nbremond77/Autoduino/photos/IMG_6386.resized.JPG

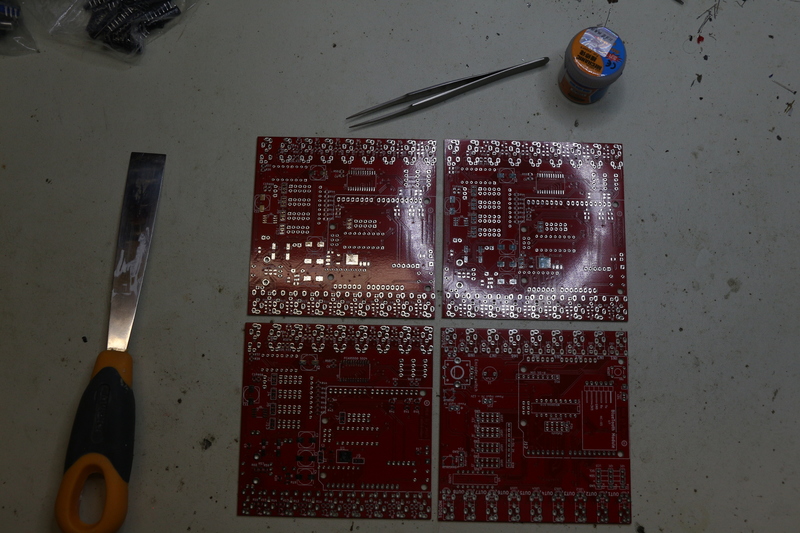
photos/IMG_6386.resized.JPG
