nbremond77/Autoduino/photos/IMG_6387.resized.JPG

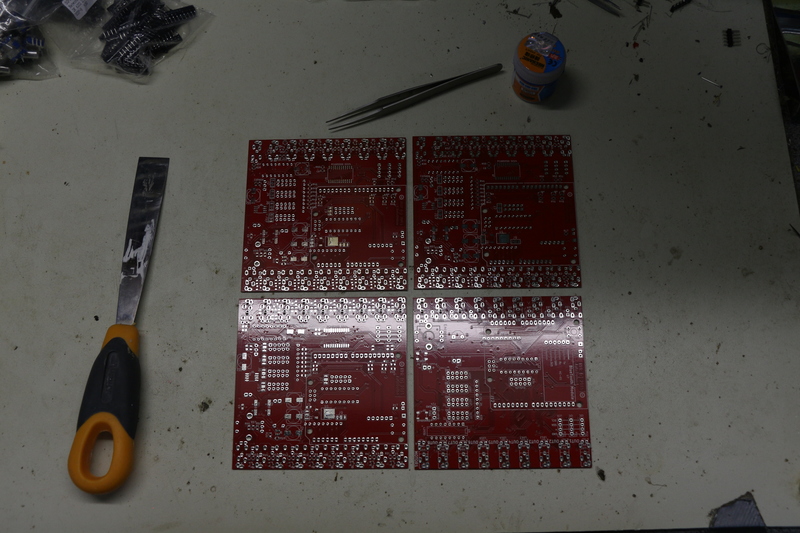
photos/IMG_6387.resized.JPG
