nbremond77/Autoduino/photos/IMG_6388.resized.JPG

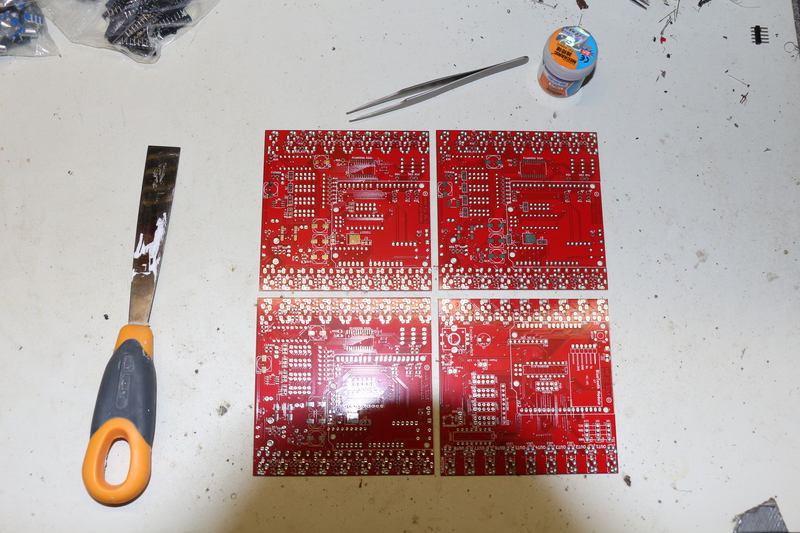
photos/IMG_6388.resized.JPG
