nbremond77/Autoduino/photos/IMG_6389.resized.JPG

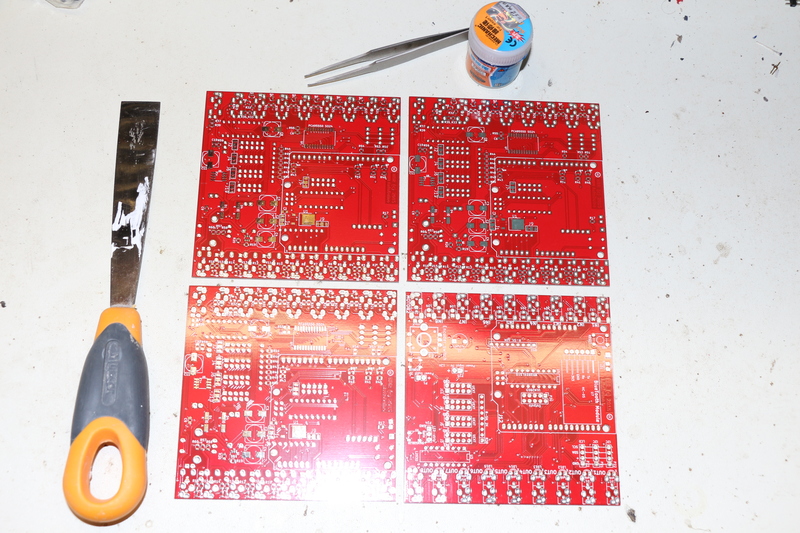
photos/IMG_6389.resized.JPG
