nbremond77/Autoduino/photos/IMG_6390.resized.JPG

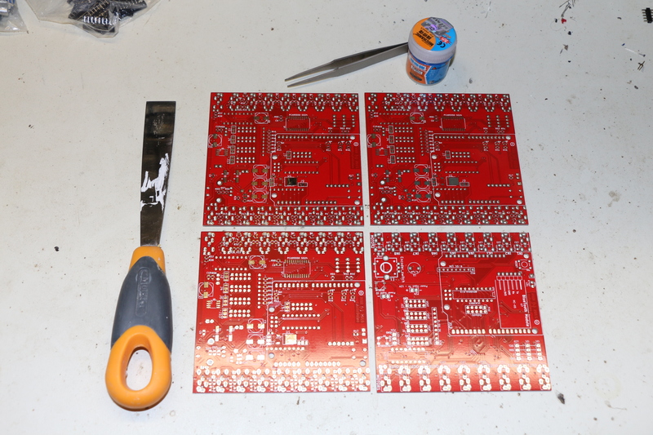
photos/IMG_6390.resized.JPG
