nbremond77/Autoduino/photos/IMG_6391.resized.JPG

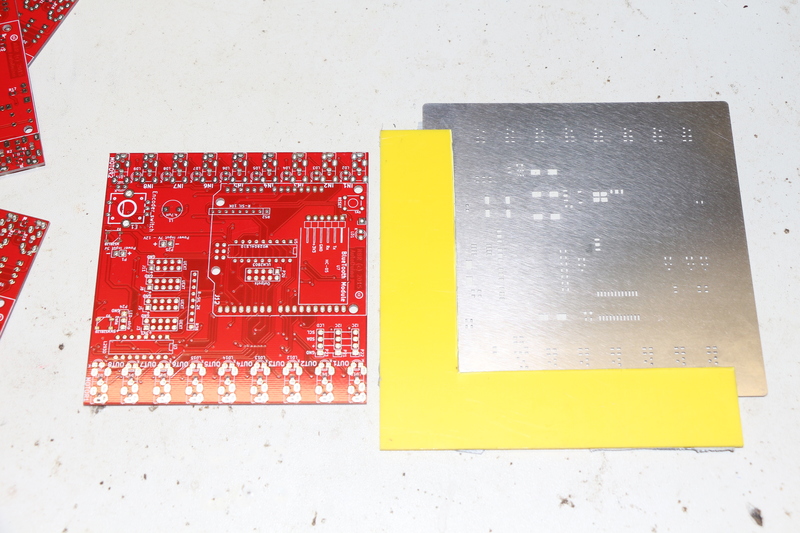
photos/IMG_6391.resized.JPG
