nbremond77/Autoduino/photos/IMG_6392.resized.JPG

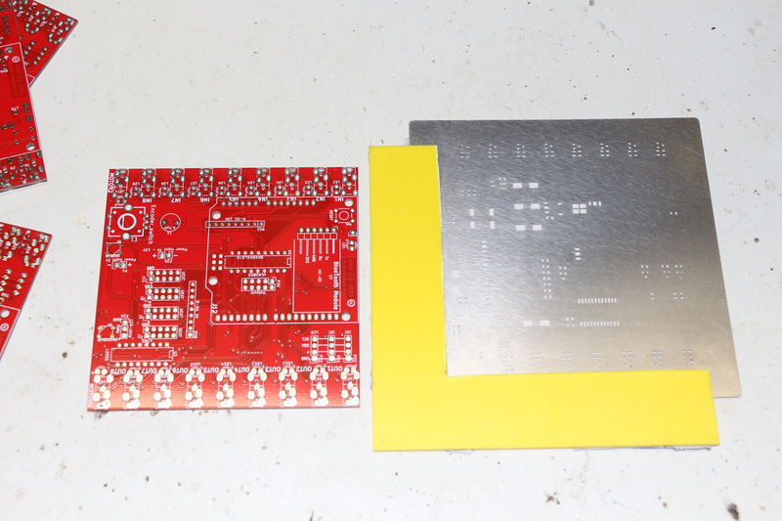
photos/IMG_6392.resized.JPG
