nbremond77/Autoduino/photos/IMG_6393.resized.JPG

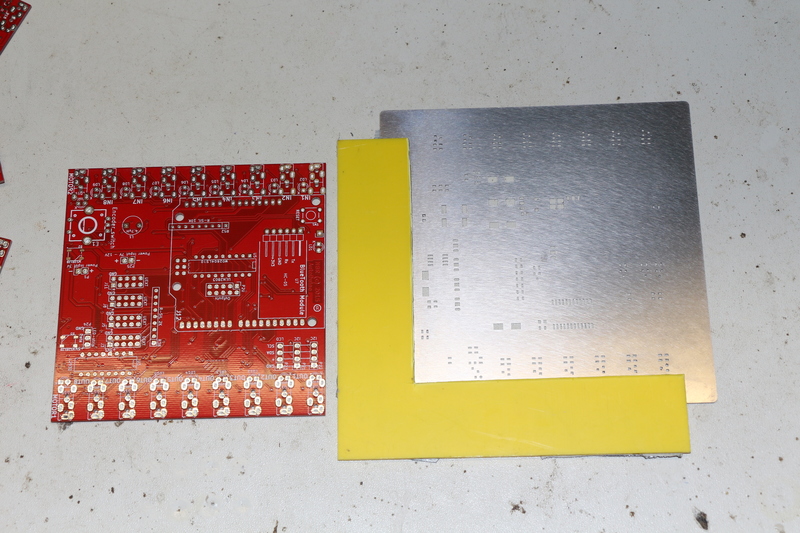
photos/IMG_6393.resized.JPG
