nbremond77/Autoduino/photos/IMG_6394.resized.JPG

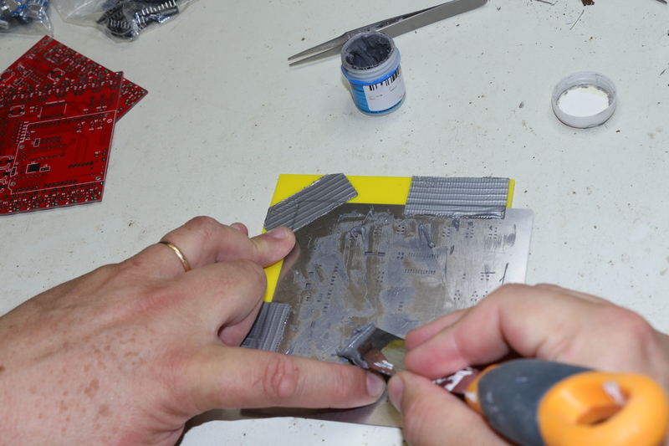
photos/IMG_6394.resized.JPG
