nbremond77/Autoduino/photos/IMG_6395.resized.JPG

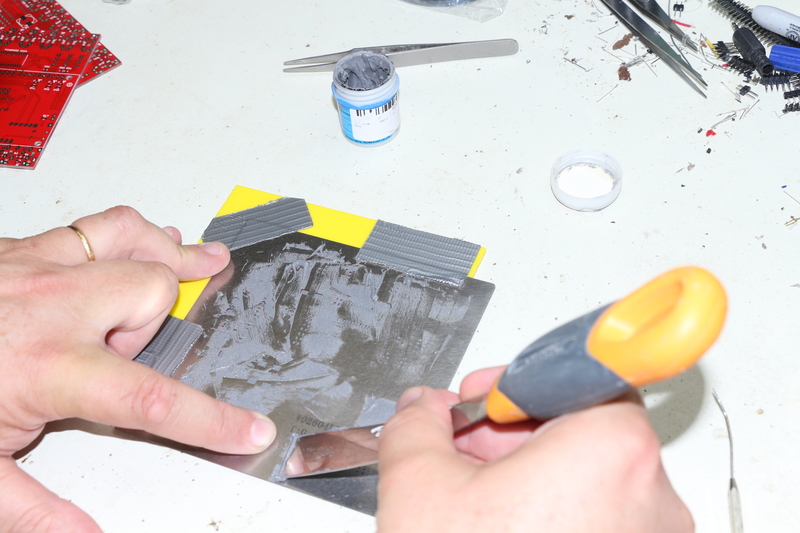
photos/IMG_6395.resized.JPG
