nbremond77/Autoduino/photos/IMG_6396.resized.JPG

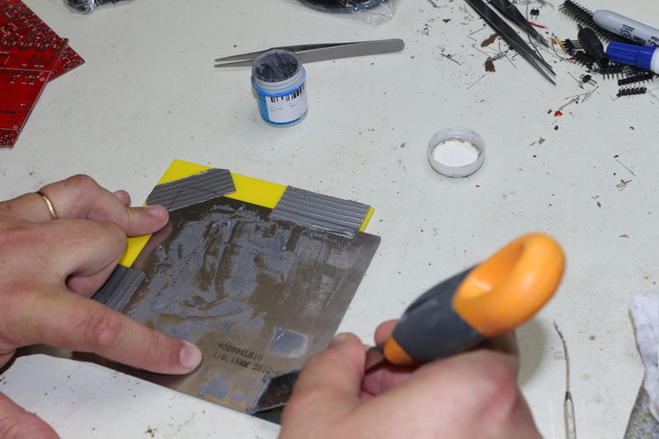
photos/IMG_6396.resized.JPG
