nbremond77/Autoduino/photos/IMG_6397.resized.JPG

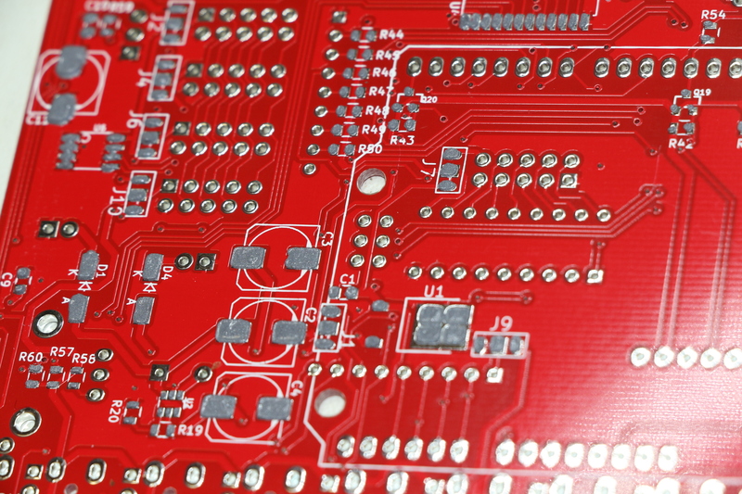
photos/IMG_6397.resized.JPG
