nbremond77/Autoduino/photos/IMG_6399.resized.JPG

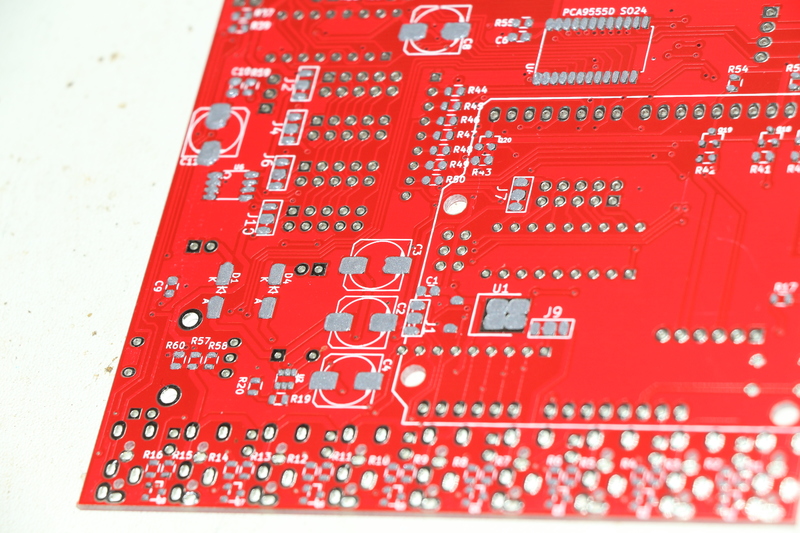
photos/IMG_6399.resized.JPG
