nbremond77/Autoduino/photos/IMG_6400.resized.JPG

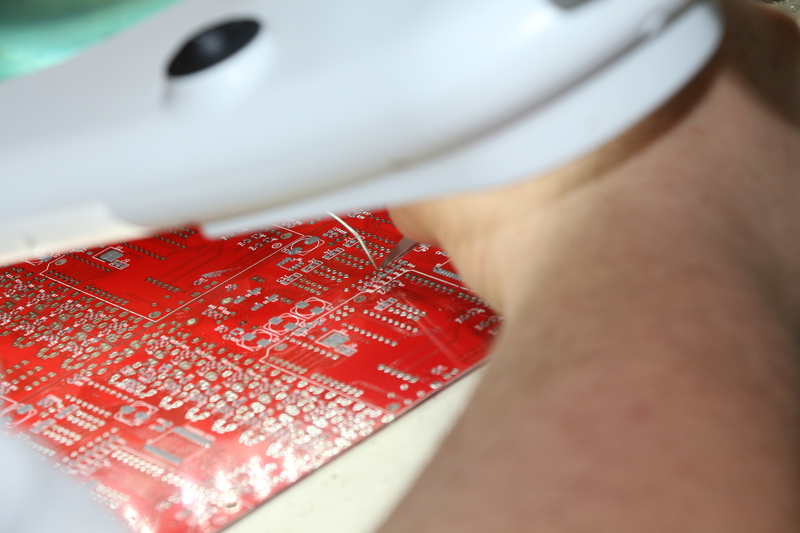
photos/IMG_6400.resized.JPG
