nbremond77/Autoduino/photos/IMG_6402.resized.JPG

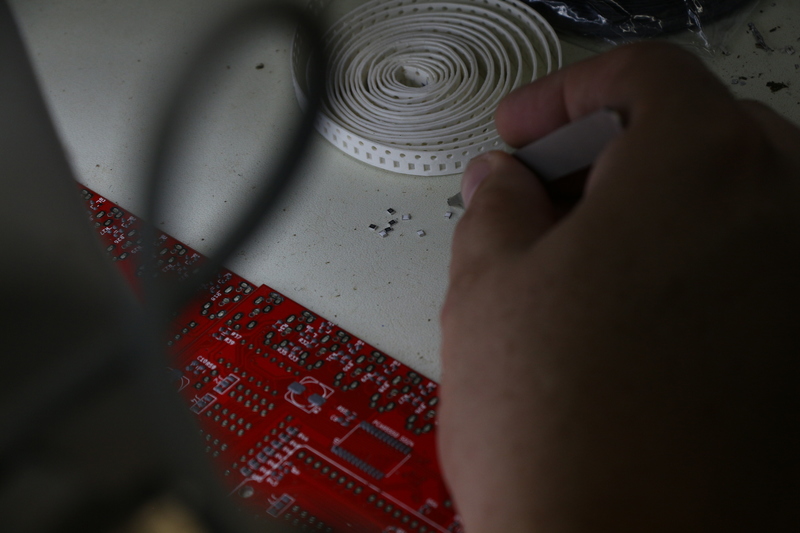
photos/IMG_6402.resized.JPG
