nbremond77/Autoduino/photos/IMG_6403.resized.JPG

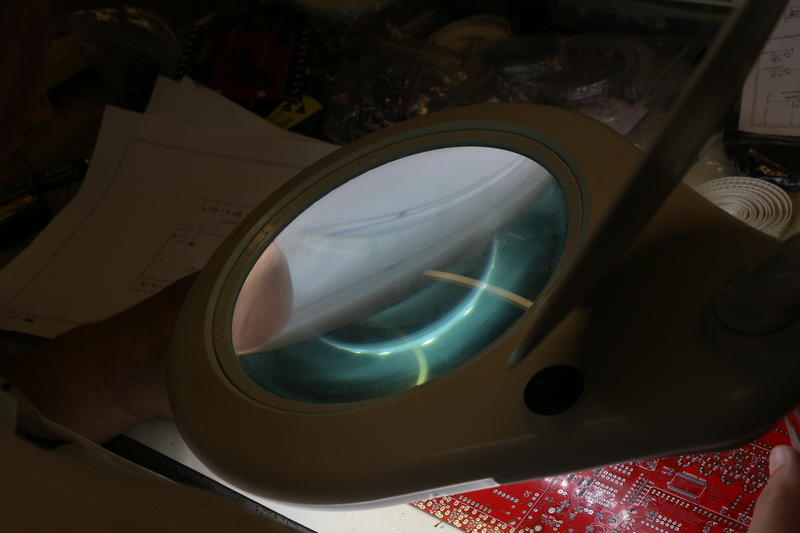
photos/IMG_6403.resized.JPG
