nbremond77/Autoduino/photos/IMG_6404.resized.JPG

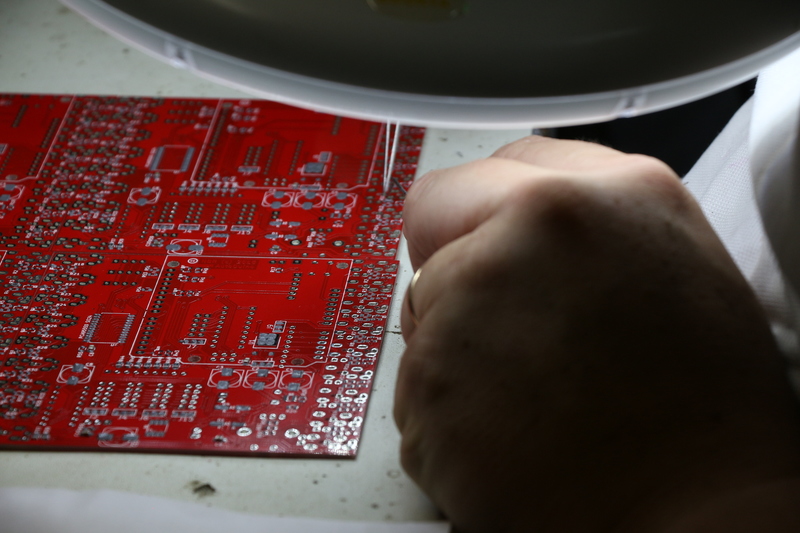
photos/IMG_6404.resized.JPG
