nbremond77/Autoduino/photos/IMG_6405.resized.JPG

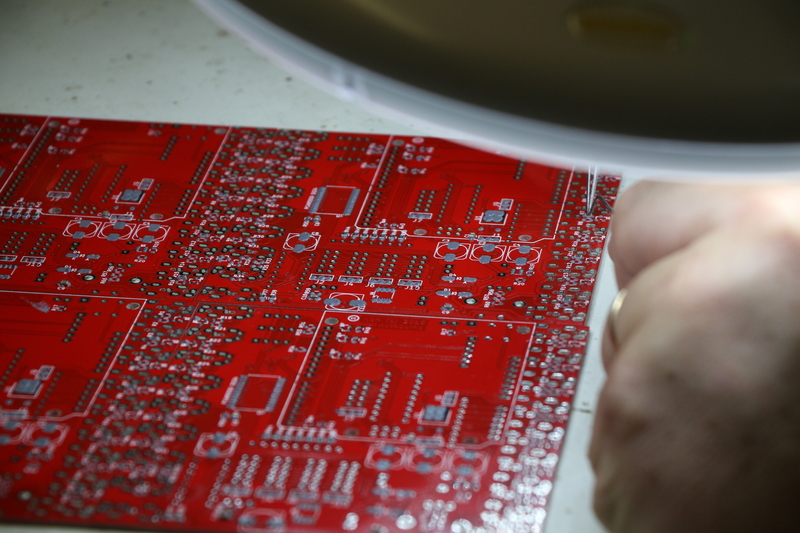
photos/IMG_6405.resized.JPG
