nbremond77/Autoduino/photos/IMG_6406.resized.JPG

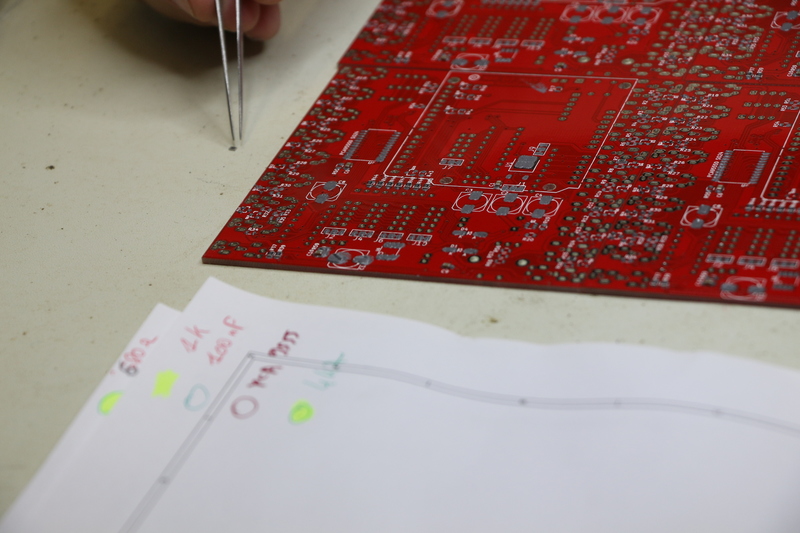
photos/IMG_6406.resized.JPG
