nbremond77/Autoduino/photos/IMG_6407.resized.JPG

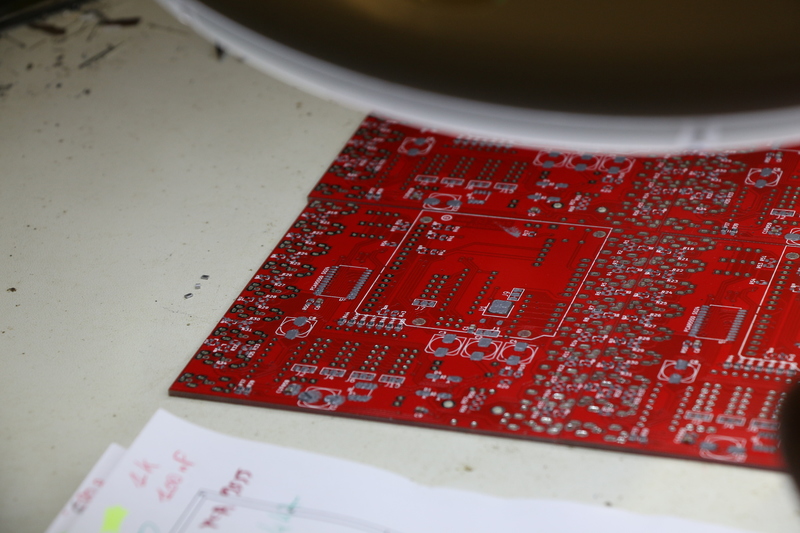
photos/IMG_6407.resized.JPG
