nbremond77/Autoduino/photos/IMG_6408.resized.JPG

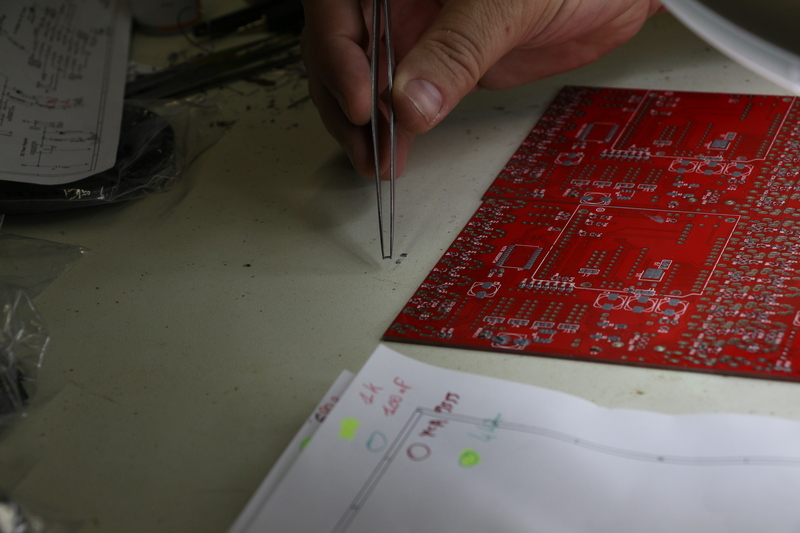
photos/IMG_6408.resized.JPG
