nbremond77/Autoduino/photos/IMG_6409.resized.JPG

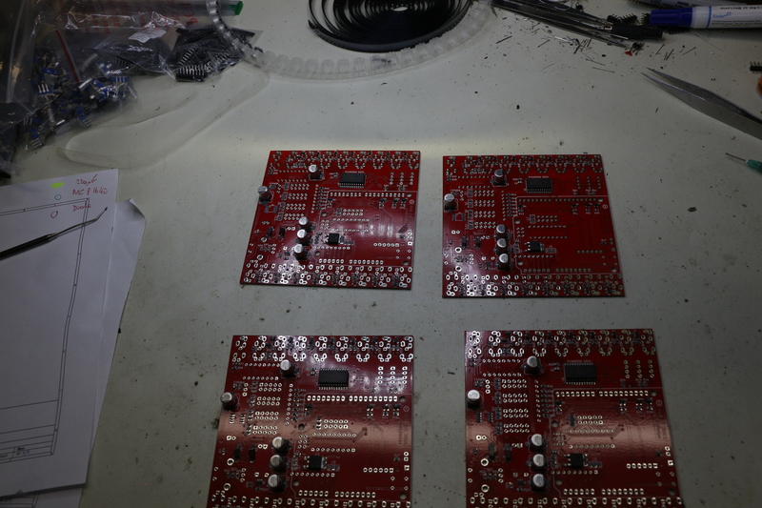
photos/IMG_6409.resized.JPG
