nbremond77/Autoduino/photos/IMG_6410.resized.JPG

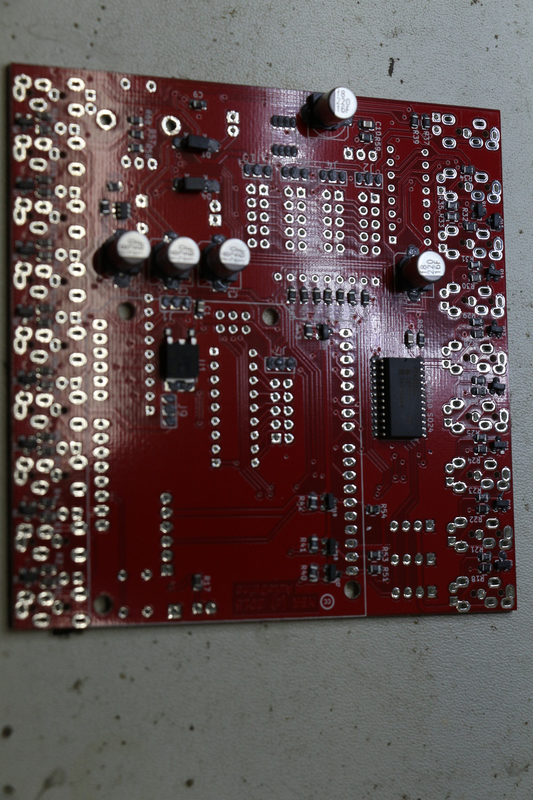
photos/IMG_6410.resized.JPG
