nbremond77/Autoduino/photos/IMG_6411.resized.JPG

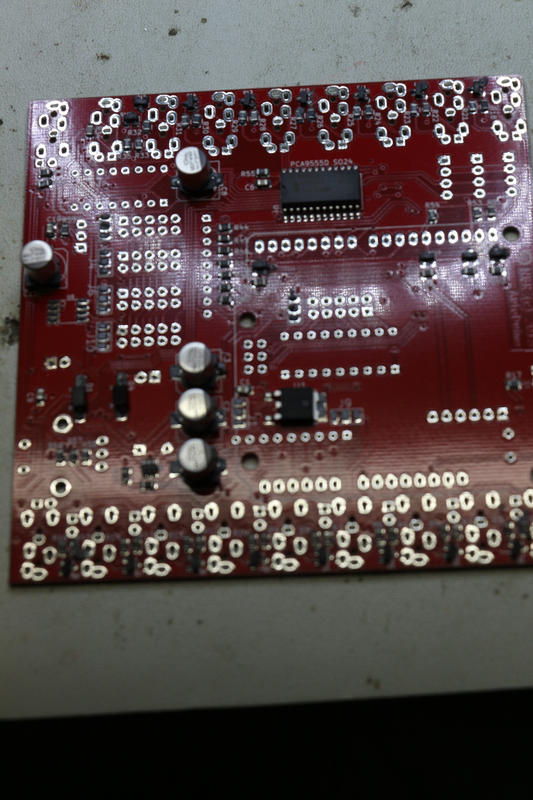
photos/IMG_6411.resized.JPG
