nbremond77/Autoduino/photos/IMG_6412.resized.JPG

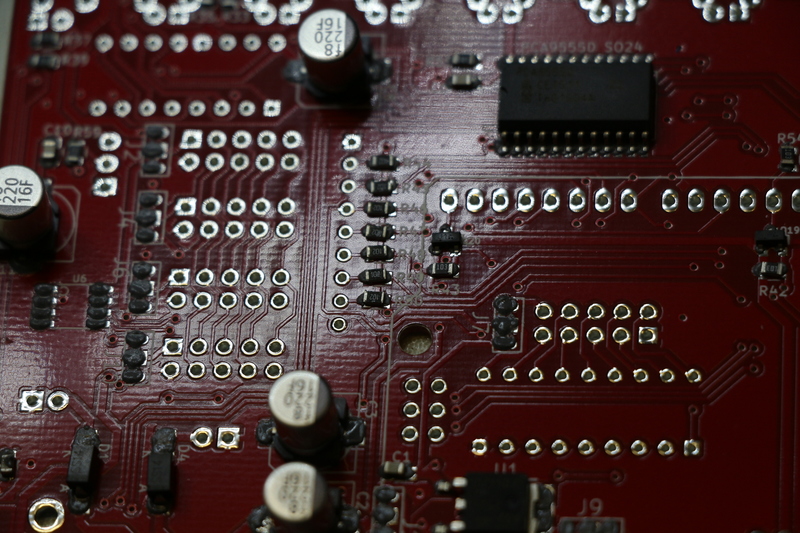
photos/IMG_6412.resized.JPG
