nbremond77/Autoduino/photos/IMG_6413.resized.JPG

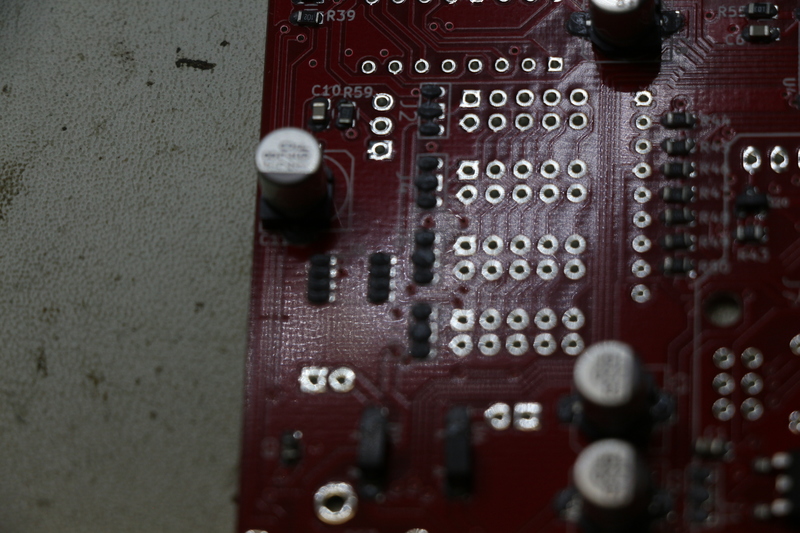
photos/IMG_6413.resized.JPG
