nbremond77/Autoduino/photos/IMG_6414.resized.JPG

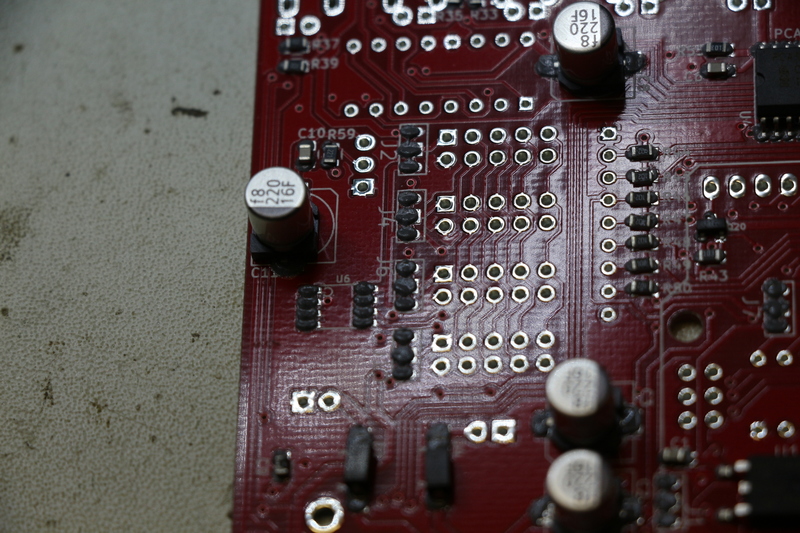
photos/IMG_6414.resized.JPG
