nbremond77/Autoduino/photos/IMG_6415.resized.JPG

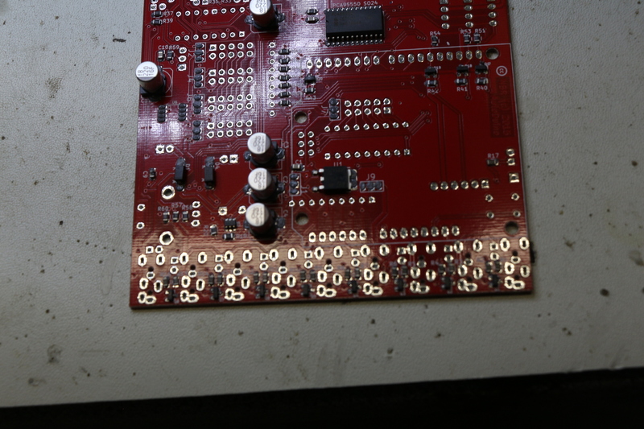
photos/IMG_6415.resized.JPG
