nbremond77/Autoduino/photos/IMG_6416.resized.JPG

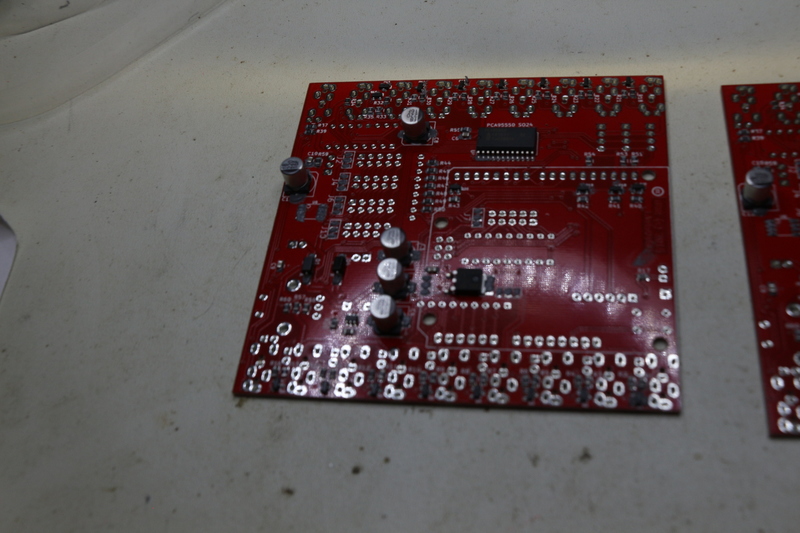
photos/IMG_6416.resized.JPG
