nbremond77/Autoduino/photos/IMG_6418.resized.JPG

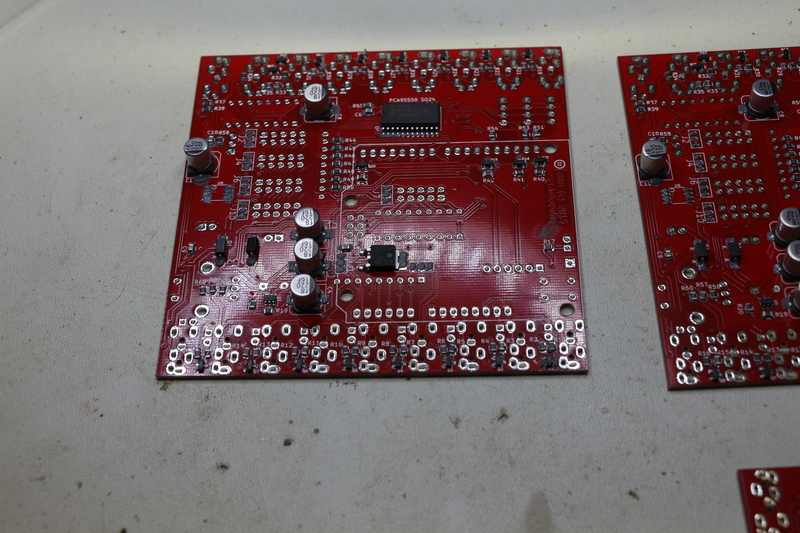
photos/IMG_6418.resized.JPG
