nbremond77/Autoduino/photos/IMG_6419.resized.JPG

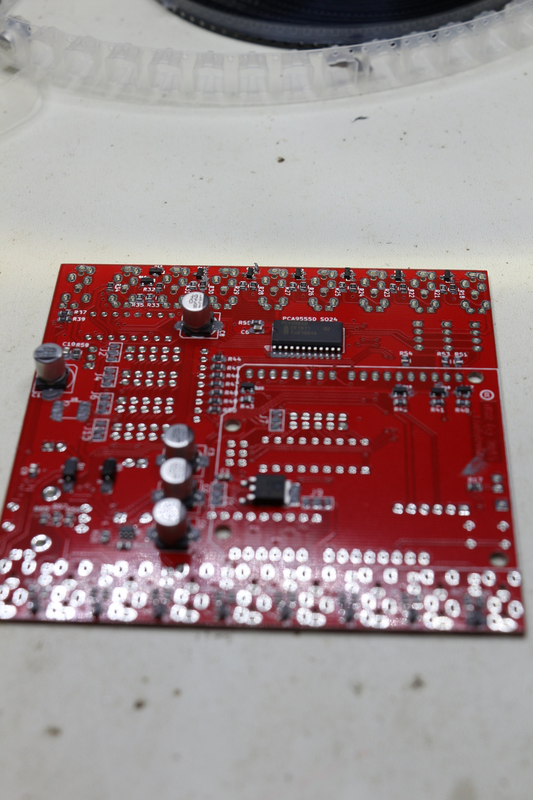
photos/IMG_6419.resized.JPG
