nbremond77/Autoduino/photos/IMG_6420.resized.JPG

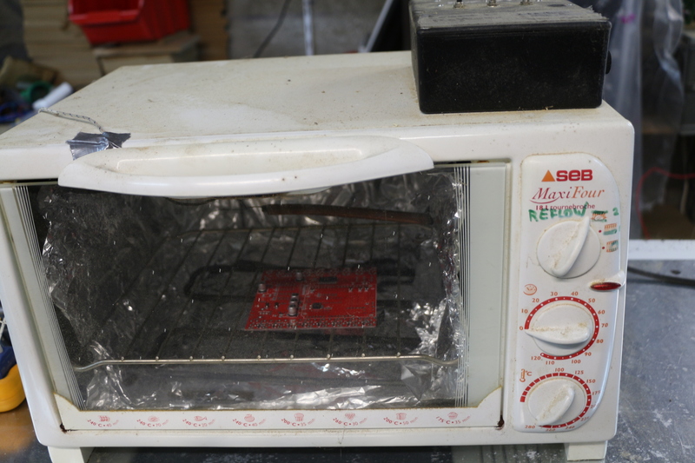
photos/IMG_6420.resized.JPG
