nbremond77/Autoduino/photos/IMG_6422.resized.JPG

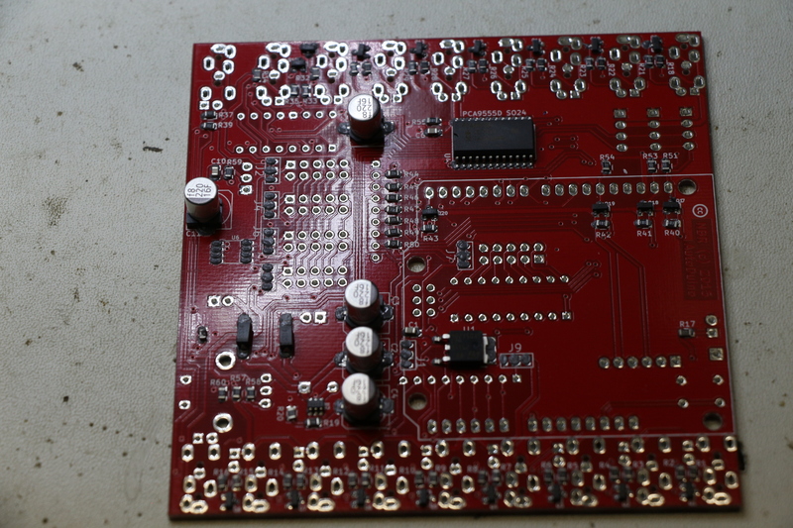
photos/IMG_6422.resized.JPG
