nbremond77/Autoduino/photos/IMG_6424.resized.JPG

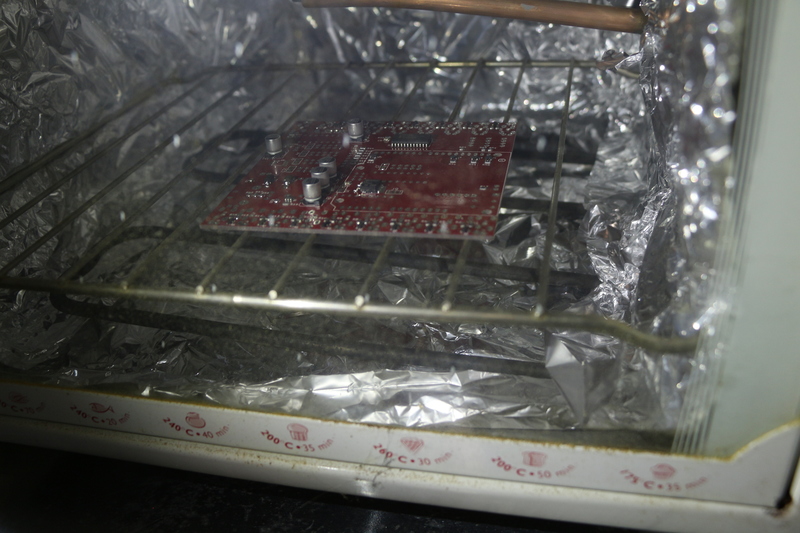
photos/IMG_6424.resized.JPG
