nbremond77/Autoduino/photos/IMG_6425.resized.JPG

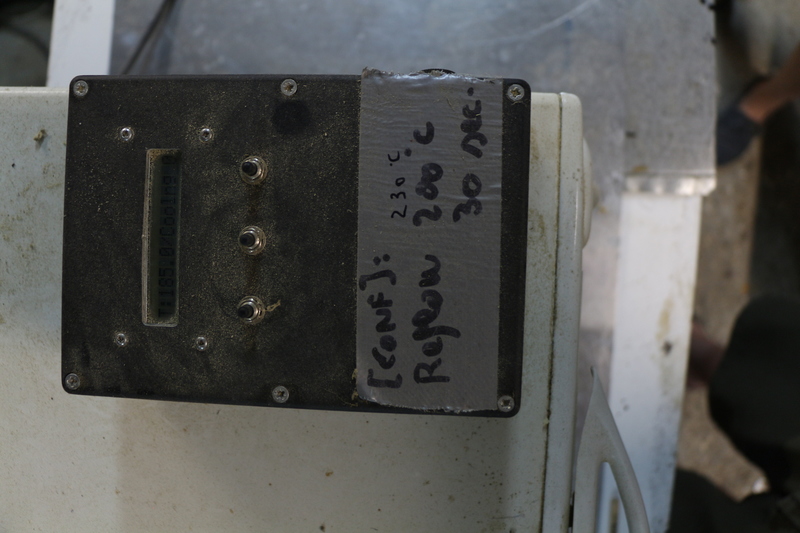
photos/IMG_6425.resized.JPG
