nbremond77/Autoduino/photos/IMG_6426.resized.JPG

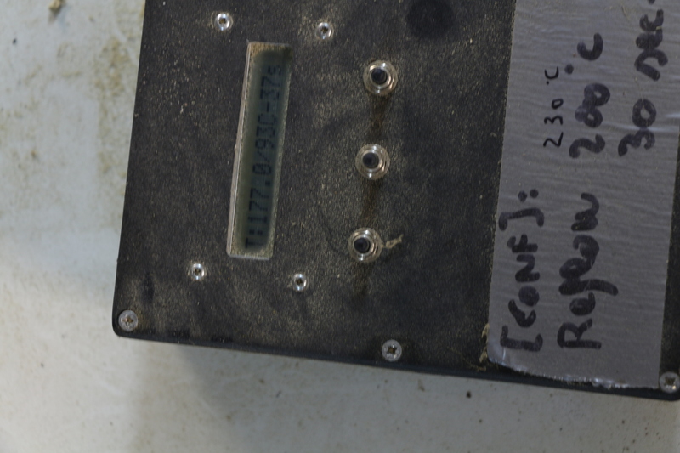
photos/IMG_6426.resized.JPG
