nbremond77/Autoduino/photos/IMG_6427.resized.JPG

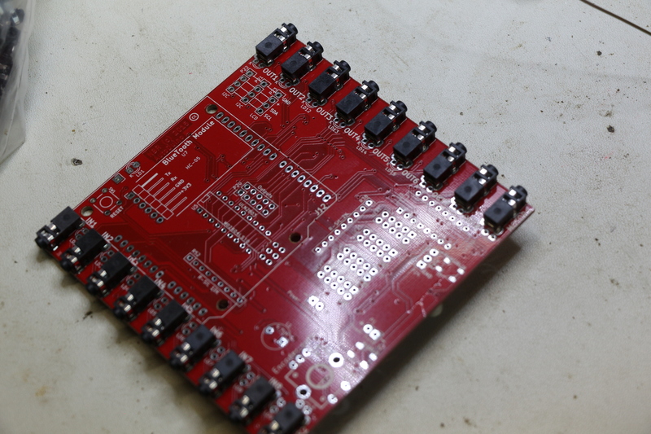
photos/IMG_6427.resized.JPG
