nbremond77/Autoduino/photos/IMG_6428.resized.JPG

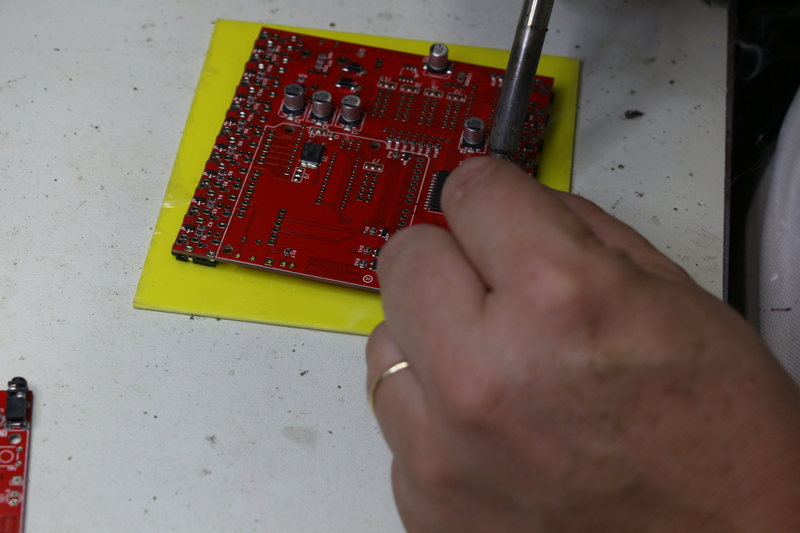
photos/IMG_6428.resized.JPG
