nbremond77/Autoduino/photos/IMG_6431.resized.JPG

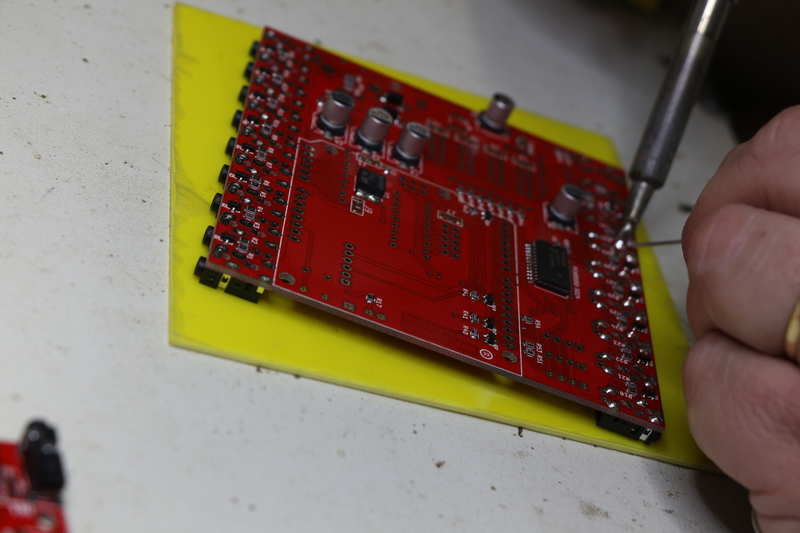
photos/IMG_6431.resized.JPG
