nbremond77/Autoduino/photos/IMG_6433.resized.JPG

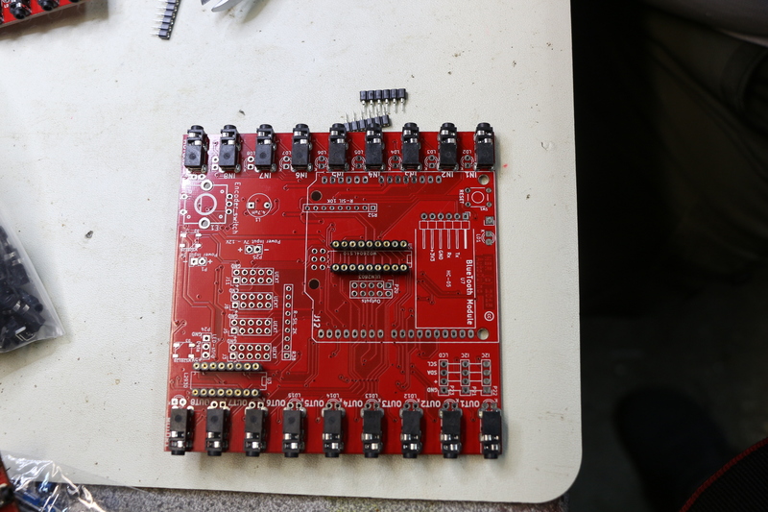
photos/IMG_6433.resized.JPG
