nbremond77/Autoduino/photos/IMG_6436.resized.JPG

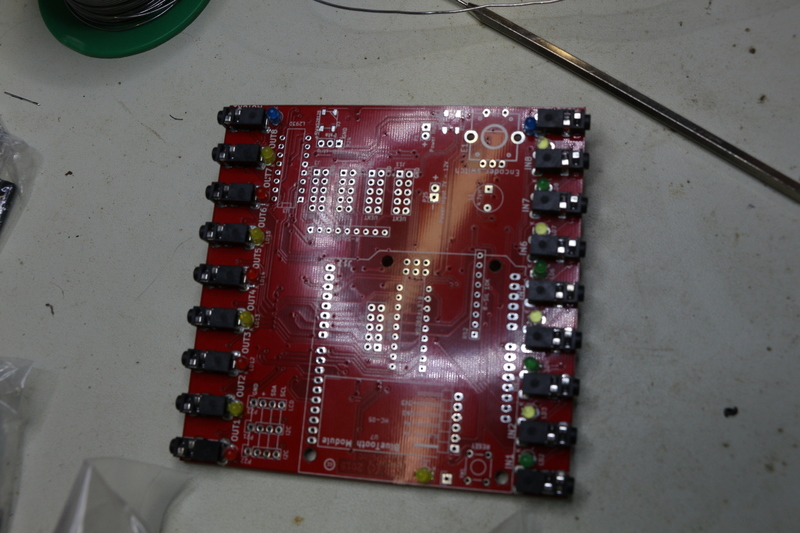
photos/IMG_6436.resized.JPG
