nbremond77/Autoduino/photos/IMG_6437.resized.JPG

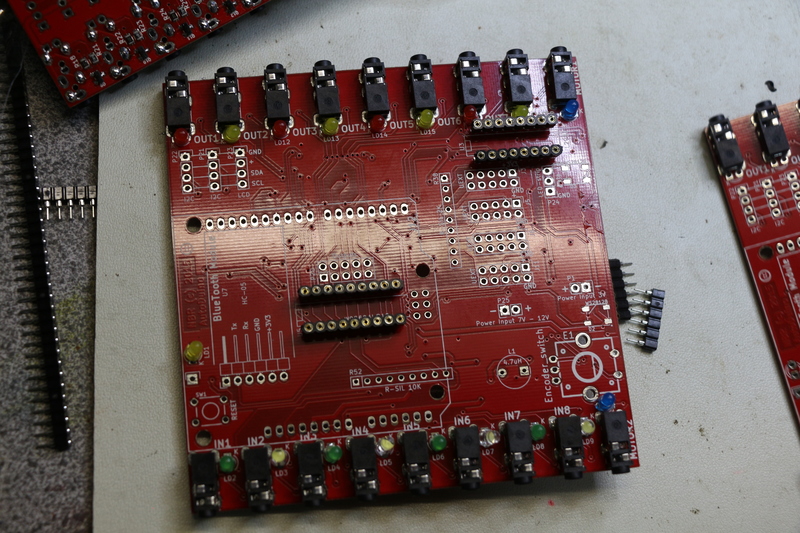
photos/IMG_6437.resized.JPG
