nbremond77/Autoduino/photos/IMG_6438.resized.JPG

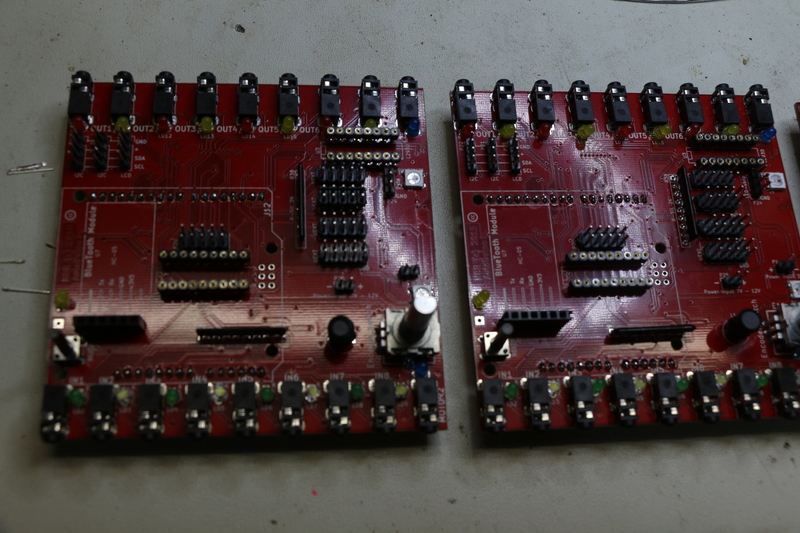
photos/IMG_6438.resized.JPG
