nbremond77/Autoduino/photos/IMG_6439.resized.JPG

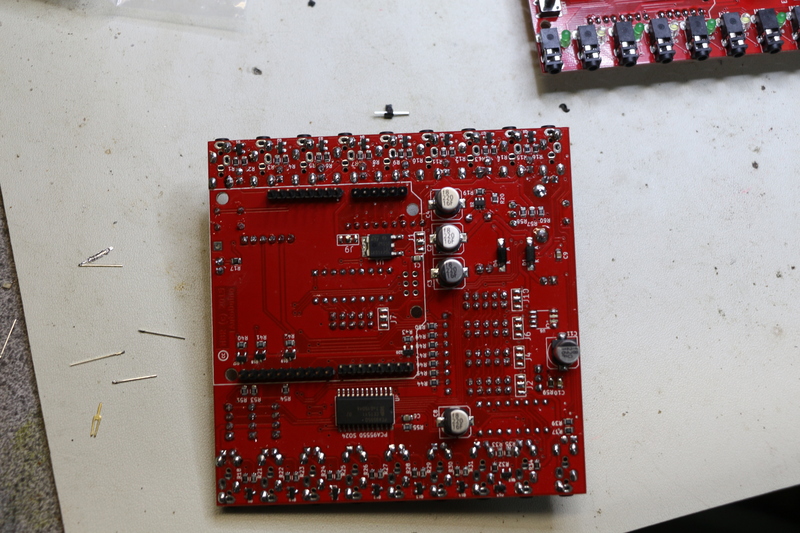
photos/IMG_6439.resized.JPG
