nbremond77/Autoduino/photos/IMG_6440.resized.JPG

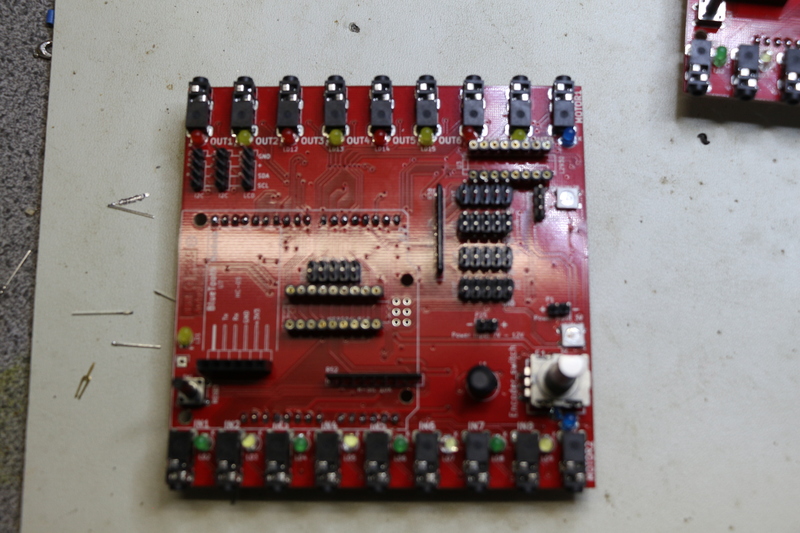
photos/IMG_6440.resized.JPG
