nbremond77/Autoduino/photos/IMG_6441.resized.JPG

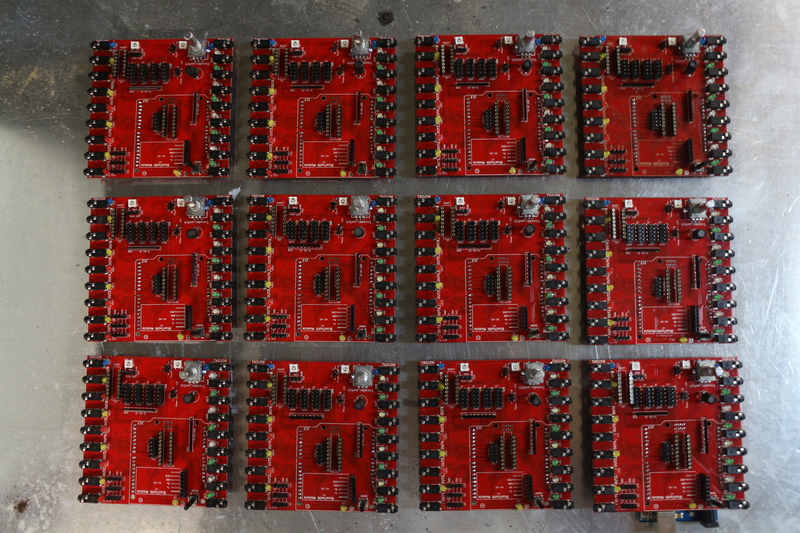
photos/IMG_6441.resized.JPG
