nbremond77/Autoduino/photos/IMG_6442.resized.JPG

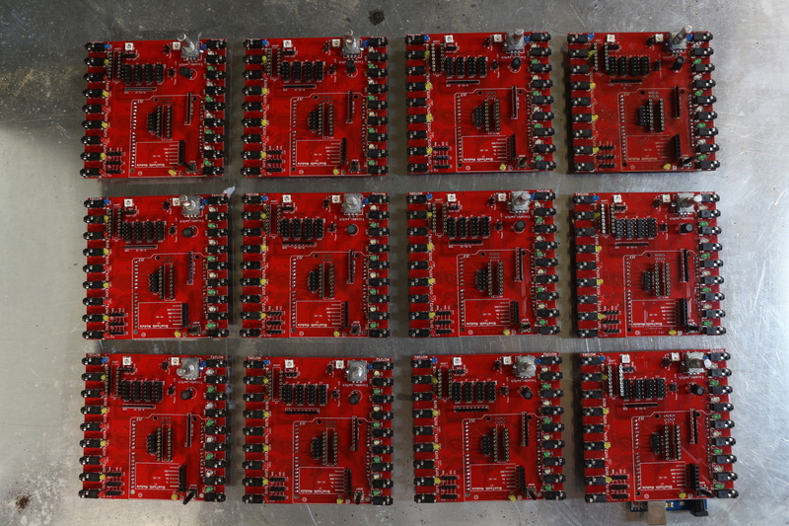
photos/IMG_6442.resized.JPG
