nbremond77/Autoduino/photos/IMG_6443.resized.JPG

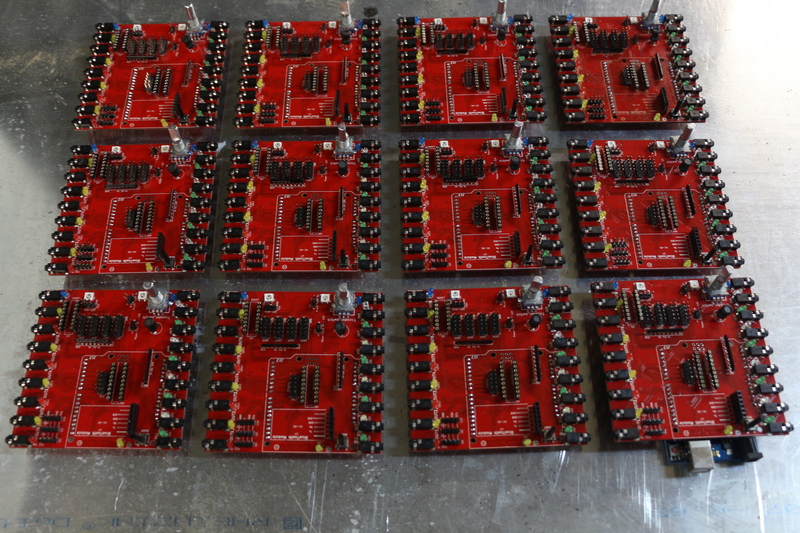
photos/IMG_6443.resized.JPG
