nbremond77/Autoduino/photos/IMG_6444.resized.JPG

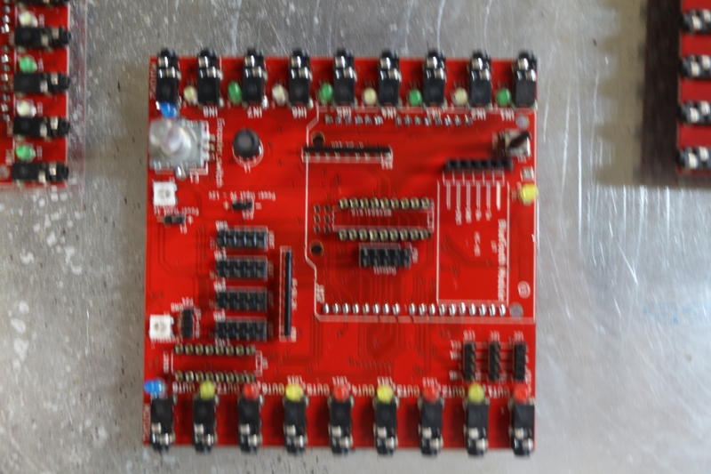
photos/IMG_6444.resized.JPG
