nbremond77/Autoduino/photos/IMG_6445.resized.JPG

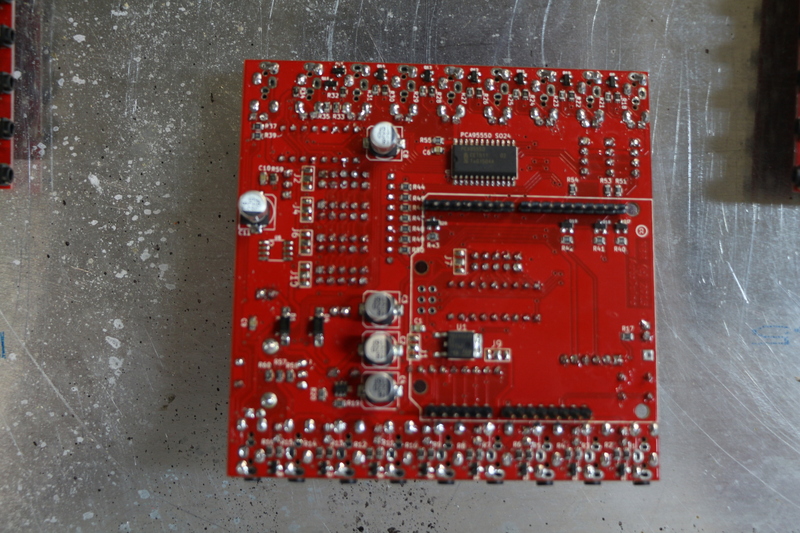
photos/IMG_6445.resized.JPG
