nbremond77/Autoduino/photos/IMG_6446.resized.JPG

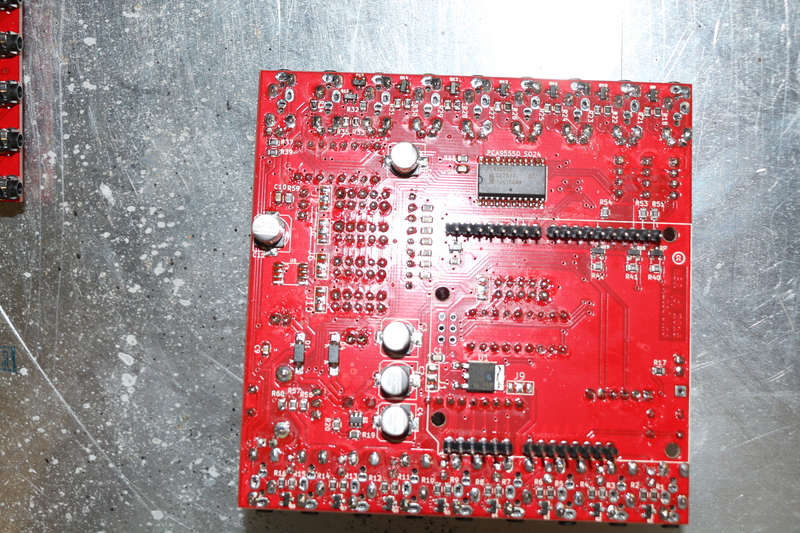
photos/IMG_6446.resized.JPG
