nbremond77/Autoduino/photos/IMG_6447.resized.JPG

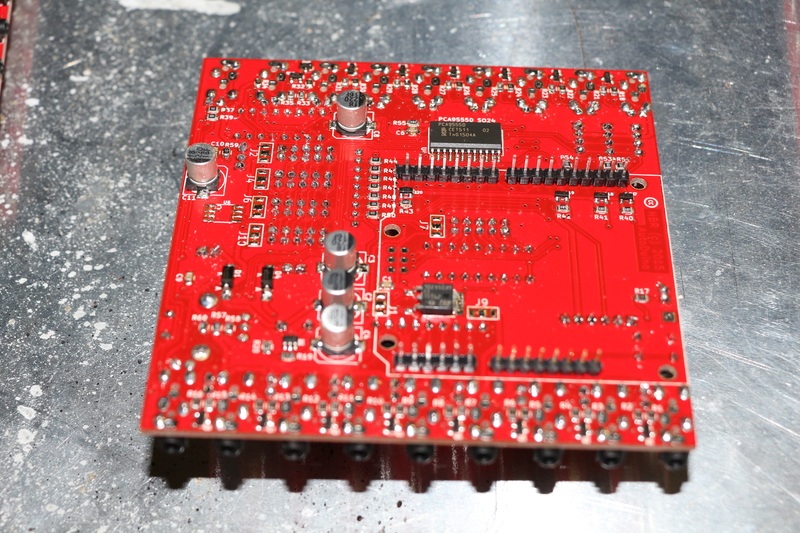
photos/IMG_6447.resized.JPG
