nbremond77/Autoduino/photos/IMG_6449.resized.JPG

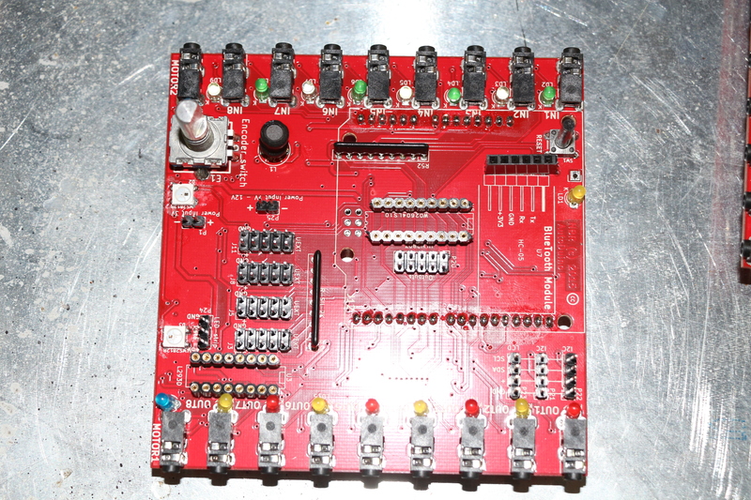
photos/IMG_6449.resized.JPG
