nbremond77/Autoduino/photos/IMG_6450.resized.JPG

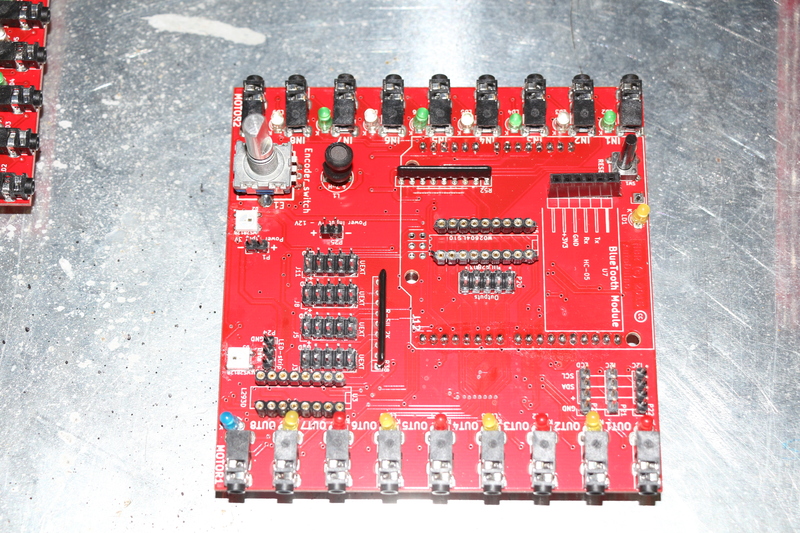
photos/IMG_6450.resized.JPG
