nbremond77/Autoduino/photos/IMG_6451.resized.JPG

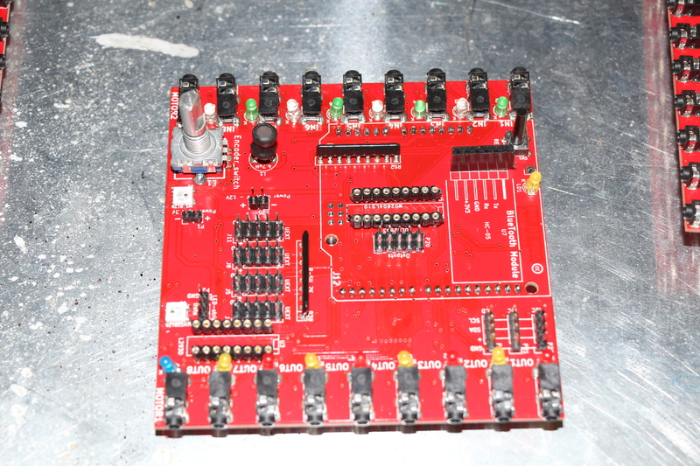
photos/IMG_6451.resized.JPG
