nbremond77/Autoduino/hardware/Output/Autoduino-rev2-F_SilkS.pdf

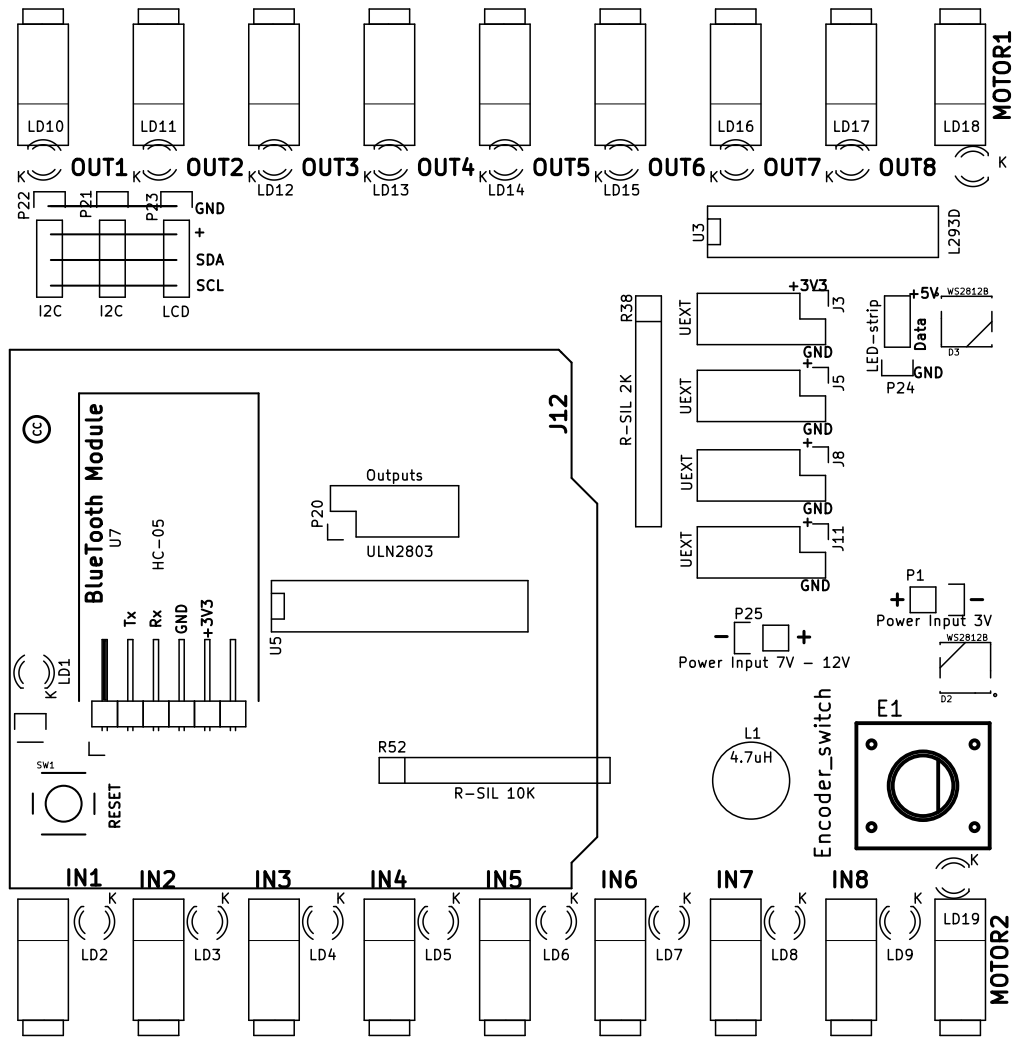
[picture p60: page 1]

BlueTooth Module RESET TxRx GND +3V3 Data +5V GND

+3V3 GND GND GND GND
